hasanalpdoyduk/Test-Software-and-Bootloader-Development-for-an-ECU/Images/dspic_applicationc.pdf

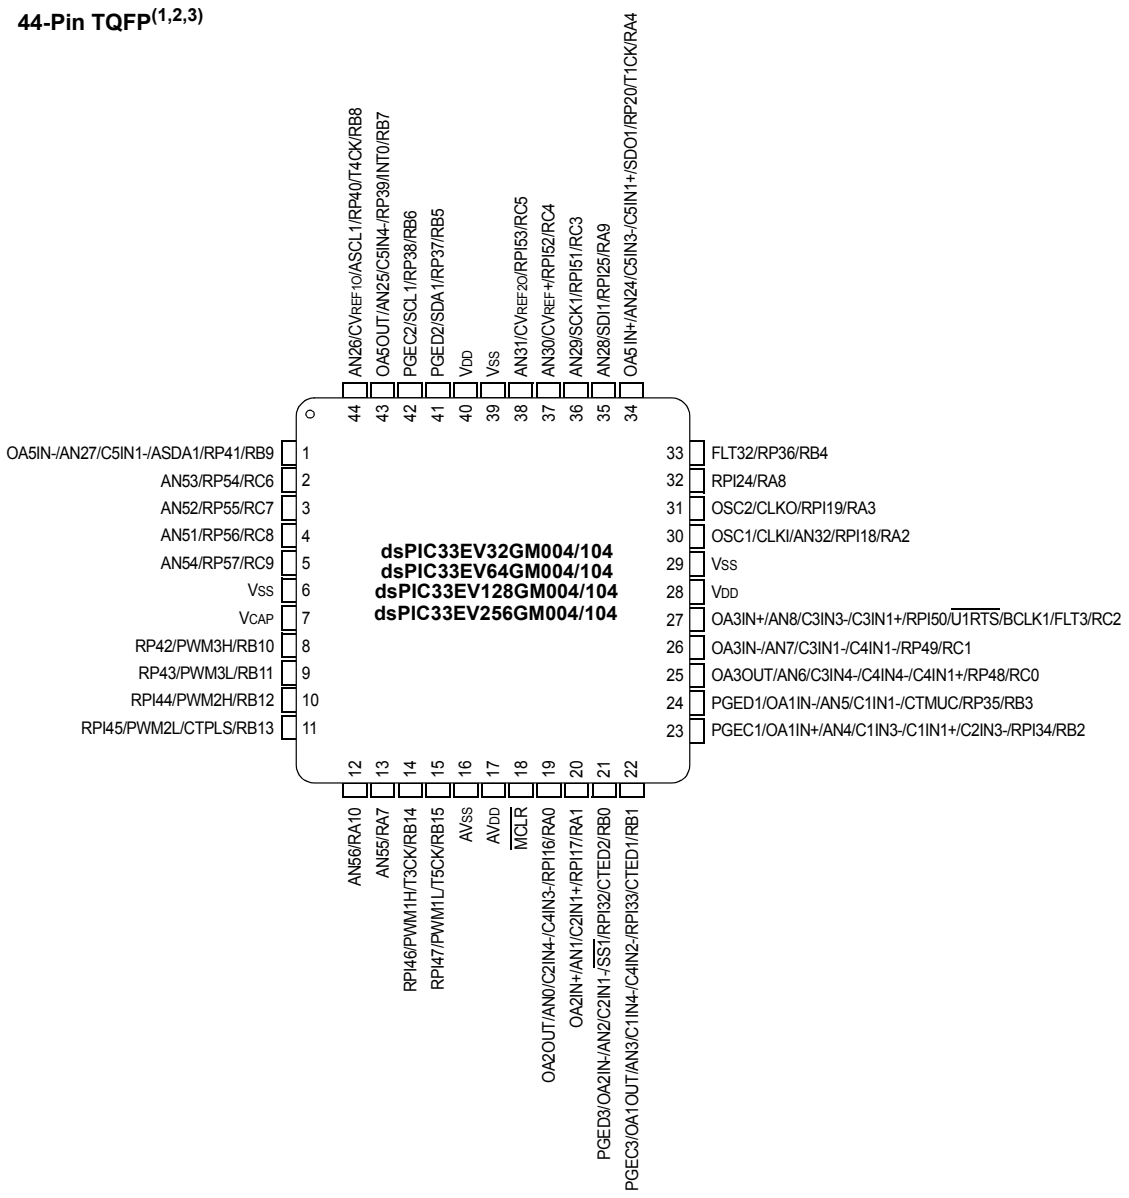
[picture p2: figure]
AN26/CVREF1O/ASCL1/RP40/T4CK/RB8 AN56/RA10; RPI45/PWM2L/CTPLS/RB13; PGEC1/OA1IN+/AN4/C1IN3-/C1IN1+/C2IN3-/RPI34/RB2; PGED1/OA1IN-/AN5/C1IN1-/CTMUC/RP35/RB3; OA3OUT/AN6/C3IN4-/C4IN4-/C4IN1+/RP48/RC0; OA3IN+/AN8/C3IN3-/C3IN1+/RPI50/U1RTS/BCLK1/FLT3/RC2; VDD; OSC1/CLKI/AN32/RPI18/RA2; OSC2/CLKO/RPI19/RA3; RPI24/RA8; FLT32/RP36/RB4; RPI46/PWM1H/T3CK/RB14; RPI47/PWM1L/T5CK/RB15; AVSS; AVDD; MCLR; OA2OUT/AN0/C2IN4-/C4IN3-/RPI16/RA0; OA2IN+/AN1/C2IN1+/RPI17/RA1; PGED3/OA2IN-/AN2/C2IN1-/SS1/RPI32/CTED2/RB0; PGEC3/OA1OUT/AN3/C1IN4-/C4IN2-/RPI33/CTED1/RB1; RPI44/PWM2H/RB12; RP43/PWM3L/RB11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
