hasanalpdoyduk/Test-Software-and-Bootloader-Development-for-an-ECU/Images/layout.pdf

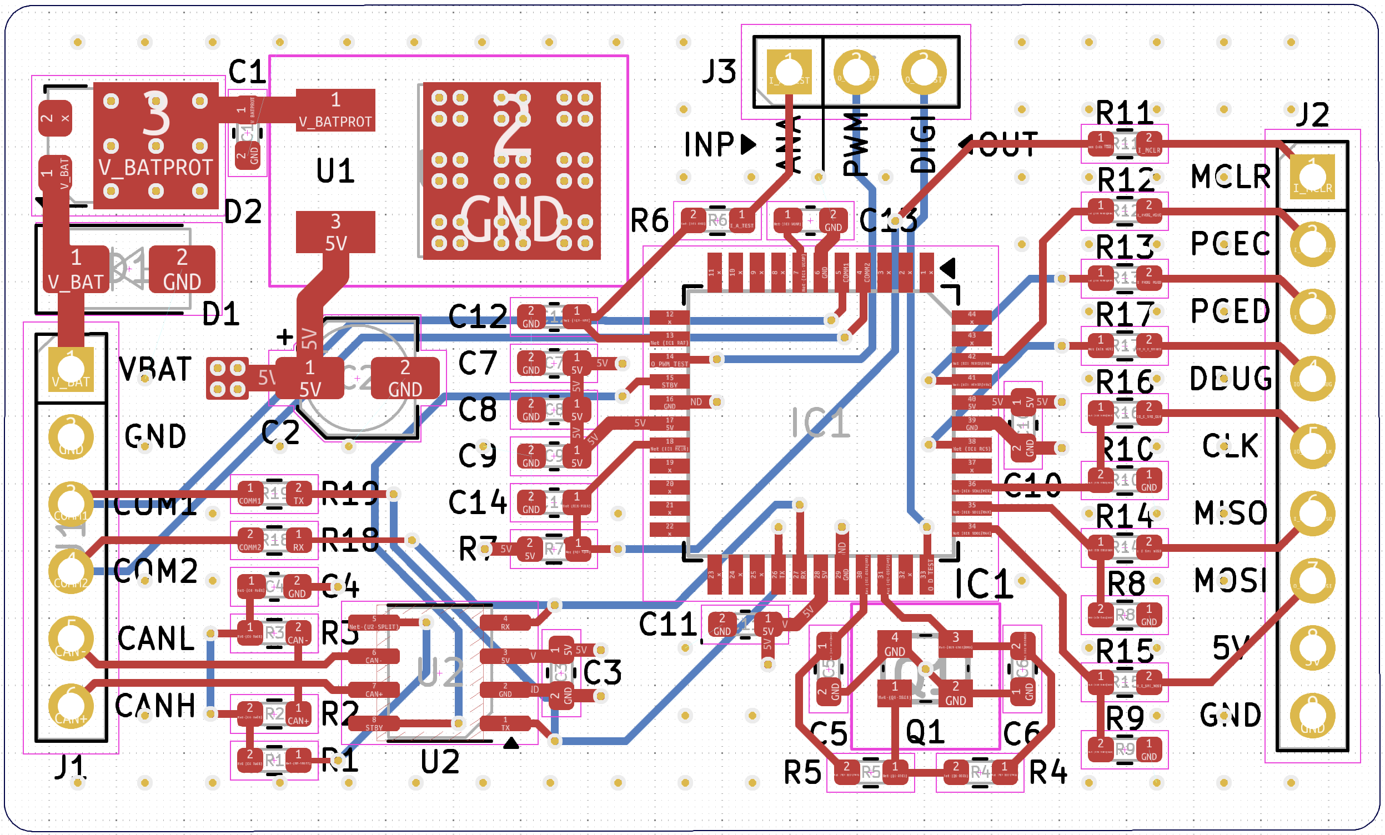
[picture p5: page 1]
