hasanalpdoyduk/Test-Software-and-Bootloader-Development-for-an-ECU/Images/pwm_wide.pdf

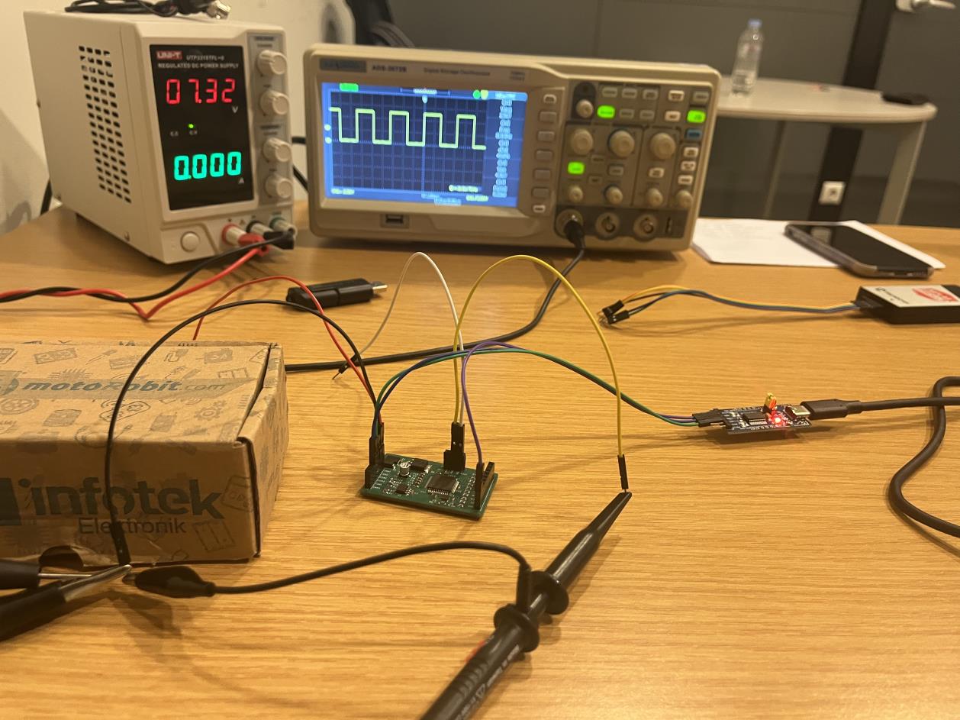
[picture p6: page 1]
