hasanalpdoyduk/Test-Software-and-Bootloader-Development-for-an-ECU/Images/rb4high_multimetre.pdf

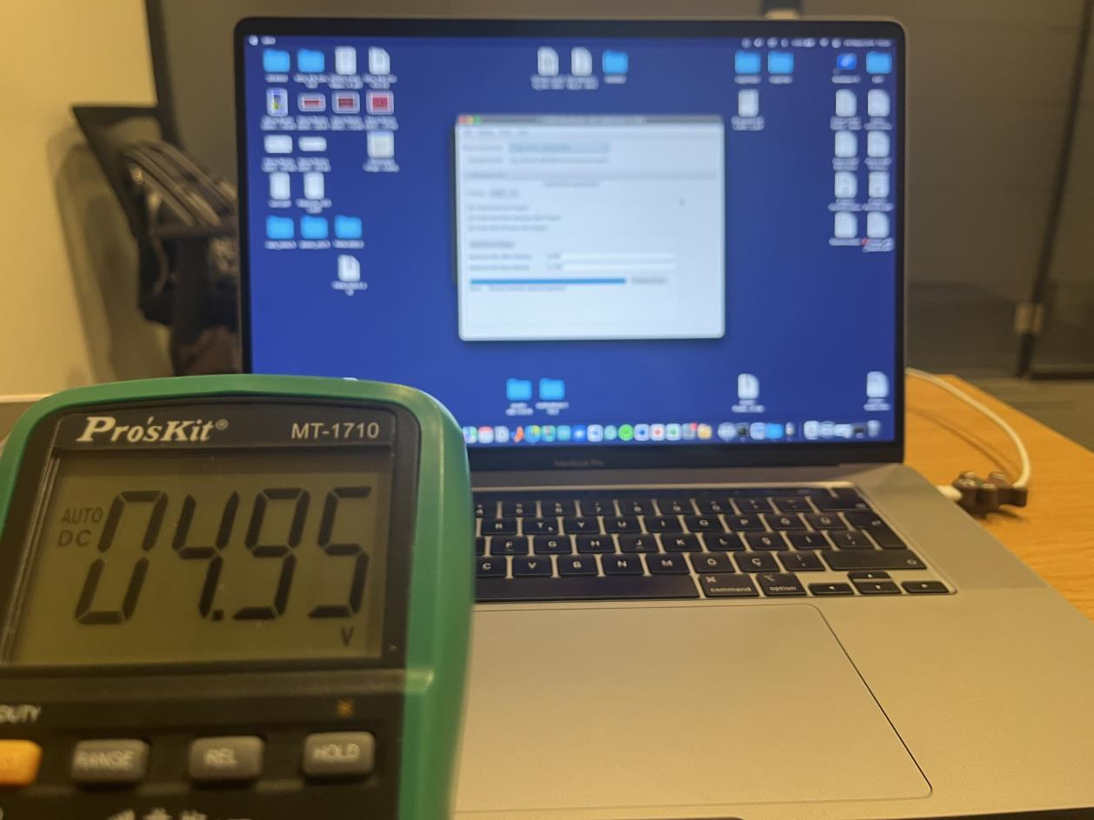
[picture p7: page 1]
