hasanalpdoyduk/Test-Software-and-Bootloader-Development-for-an-ECU/Images/rb4high_osc.pdf

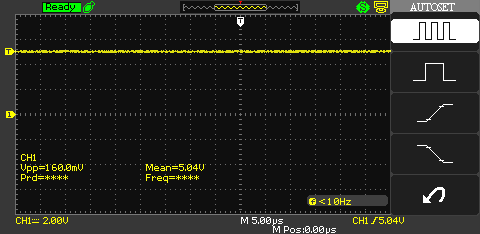
[picture p8: page 1]
