hasanalpdoyduk/Test-Software-and-Bootloader-Development-for-an-ECU/Images/simulink_0v_scope.pdf

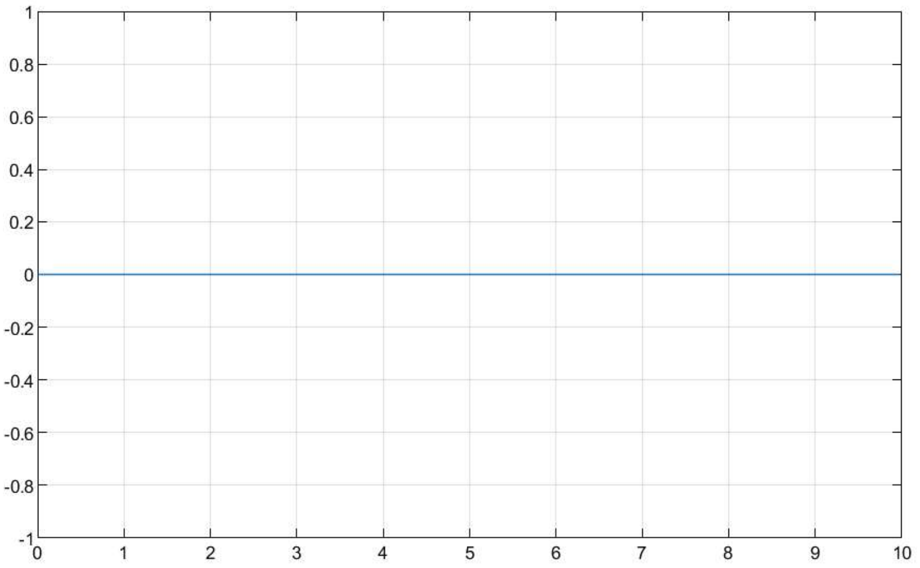
[picture p9: page 1]
