hasanalpdoyduk/Test-Software-and-Bootloader-Development-for-an-ECU/Images/simulink_5v_scope.pdf

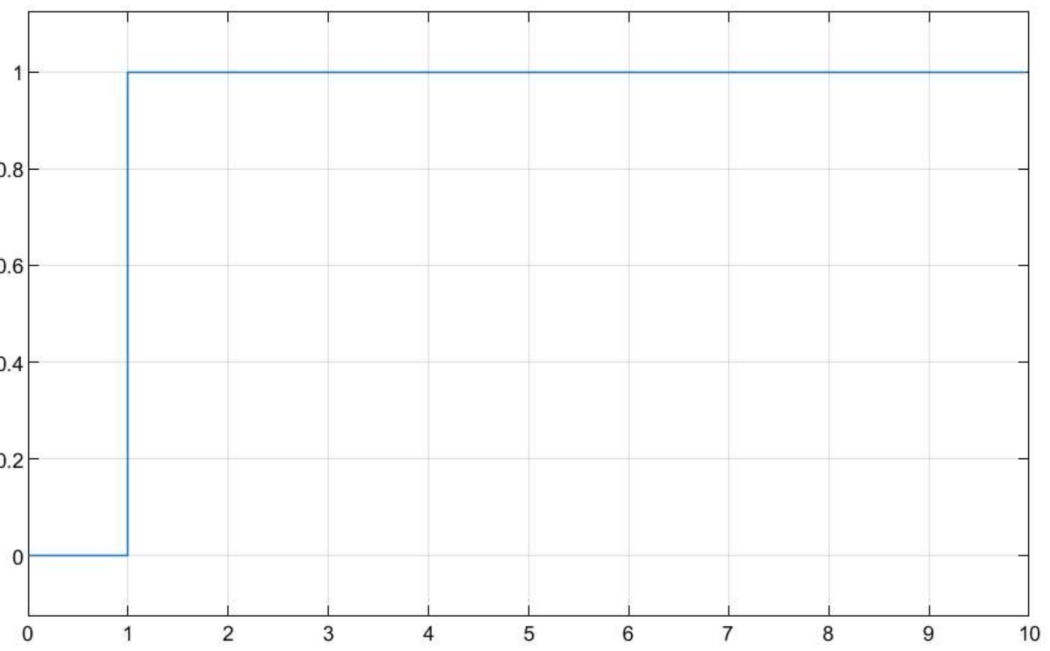
[picture p10: page 1]
