hasanalpdoyduk/Test-Software-and-Bootloader-Development-for-an-ECU/Images/basic_arch.png

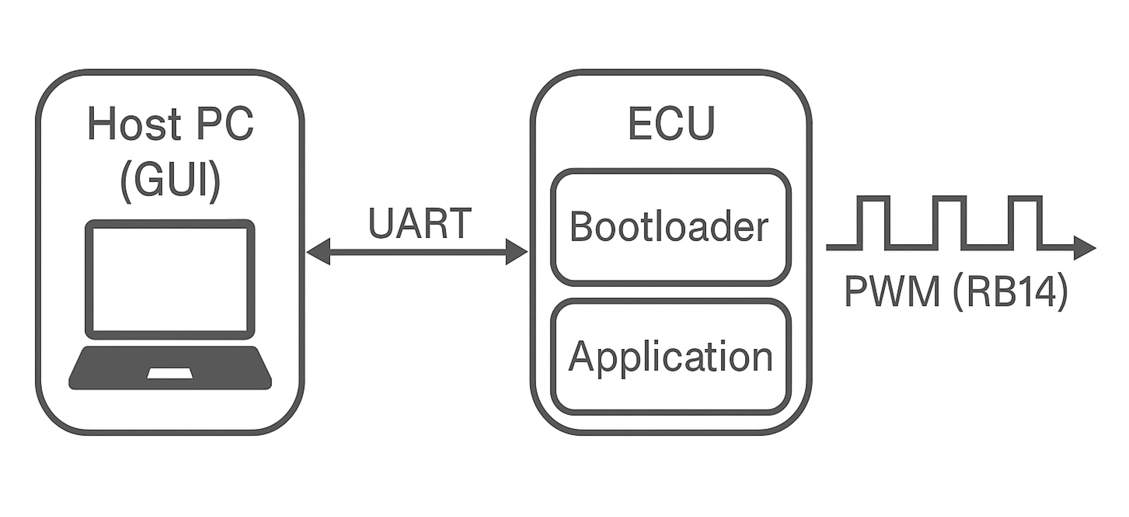
Images/basic_arch.png
