hasanalpdoyduk/Test-Software-and-Bootloader-Development-for-an-ECU/Images/board.jpg

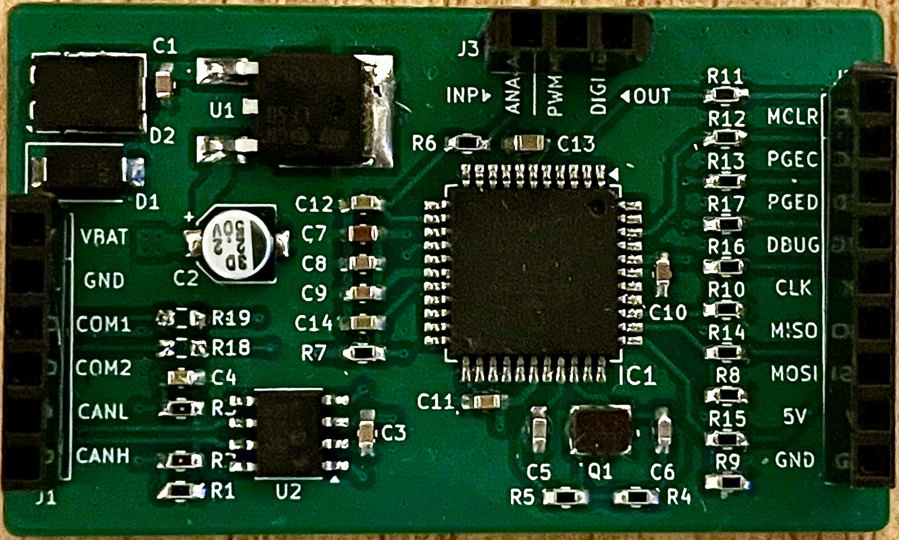
Images/board.jpg
