hasanalpdoyduk/Test-Software-and-Bootloader-Development-for-an-ECU/Images/OscillatorSs/ADS00005.BMP

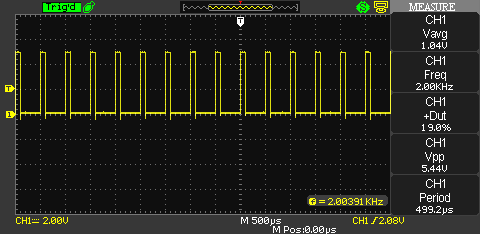
Images/OscillatorSs/ADS00005.BMP
