hasanalpdoyduk/Test-Software-and-Bootloader-Development-for-an-ECU/Images/OscillatorSs/ADS00006.BMP

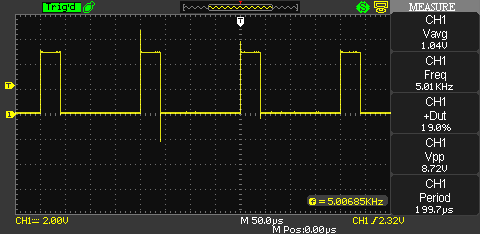
Images/OscillatorSs/ADS00006.BMP
