hasanalpdoyduk/Test-Software-and-Bootloader-Development-for-an-ECU/Images/terminal_serial_connection.png

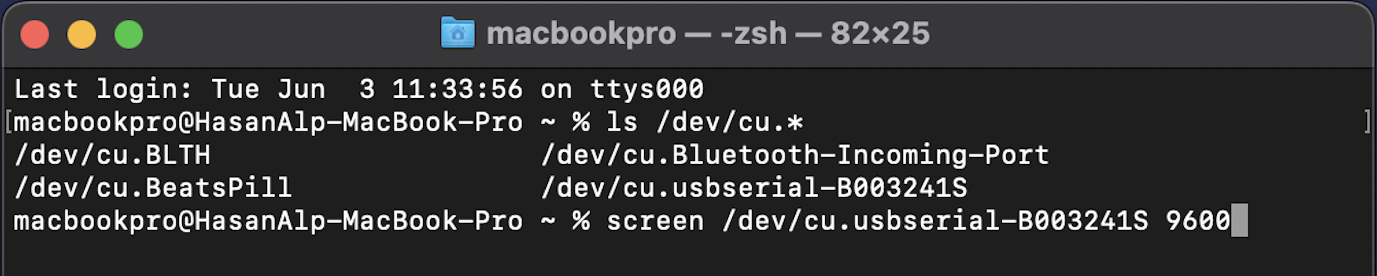
Images/terminal_serial_connection.png
