hasanalpdoyduk/Test-Software-and-Bootloader-Development-for-an-ECU/Images/terminal_UBHA_connection.png

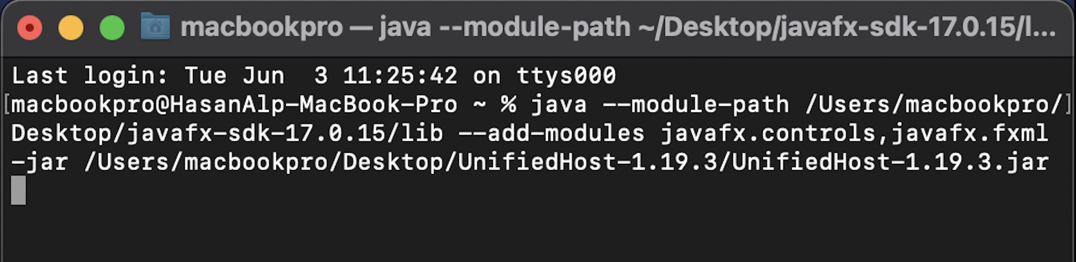
Images/terminal_UBHA_connection.png
