hasanalpdoyduk/Test-Software-and-Bootloader-Development-for-an-ECU/Images/UART1.png

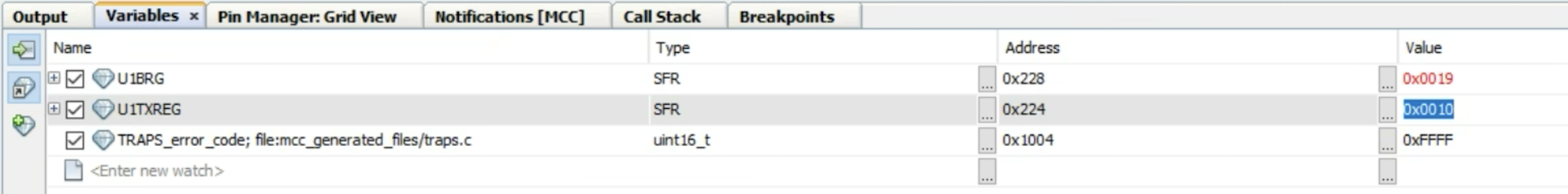
Images/UART1.png
