hasanalpdoyduk/Test-Software-and-Bootloader-Development-for-an-ECU/Images/UART_GUI_serial_port_detection.png

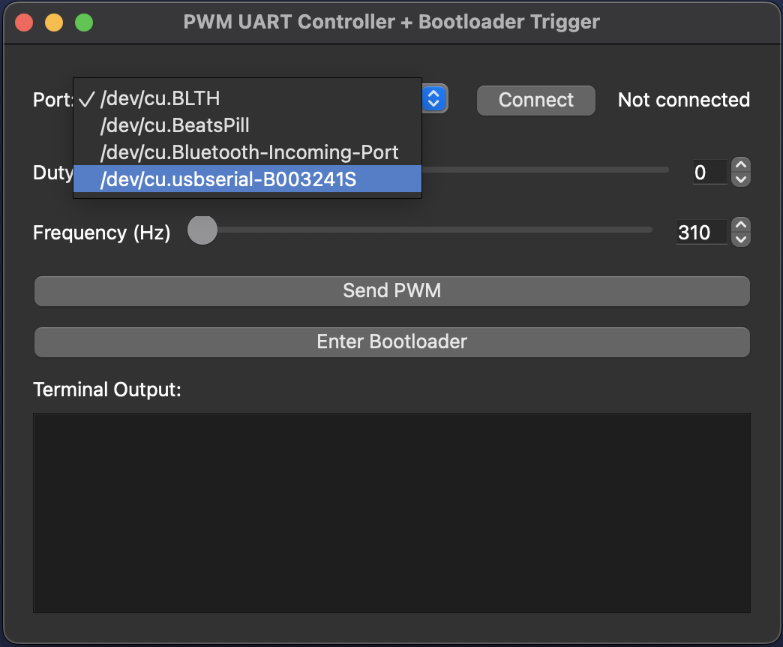
Images/UART_GUI_serial_port_detection.png
