hasanalpdoyduk/Test-Software-and-Bootloader-Development-for-an-ECU/Images/UBHA_finished.png

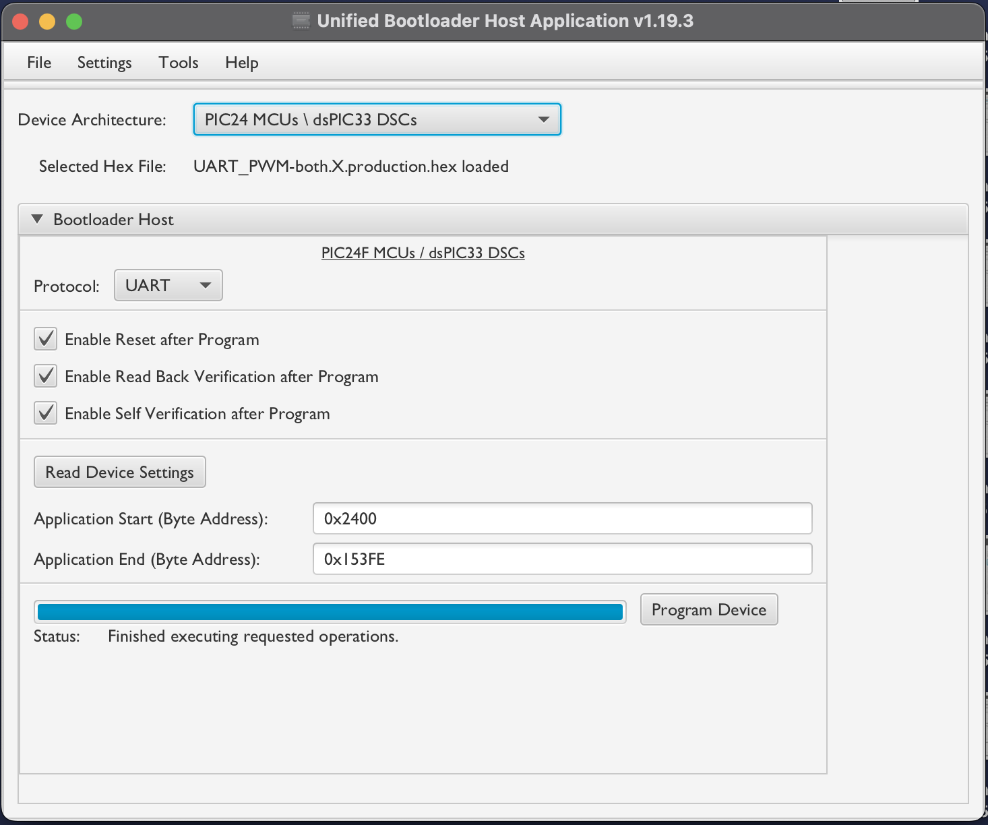
Images/UBHA_finished.png
