hasanalpdoyduk/Test-Software-and-Bootloader-Development-for-an-ECU/Images/UBHA_select1.png

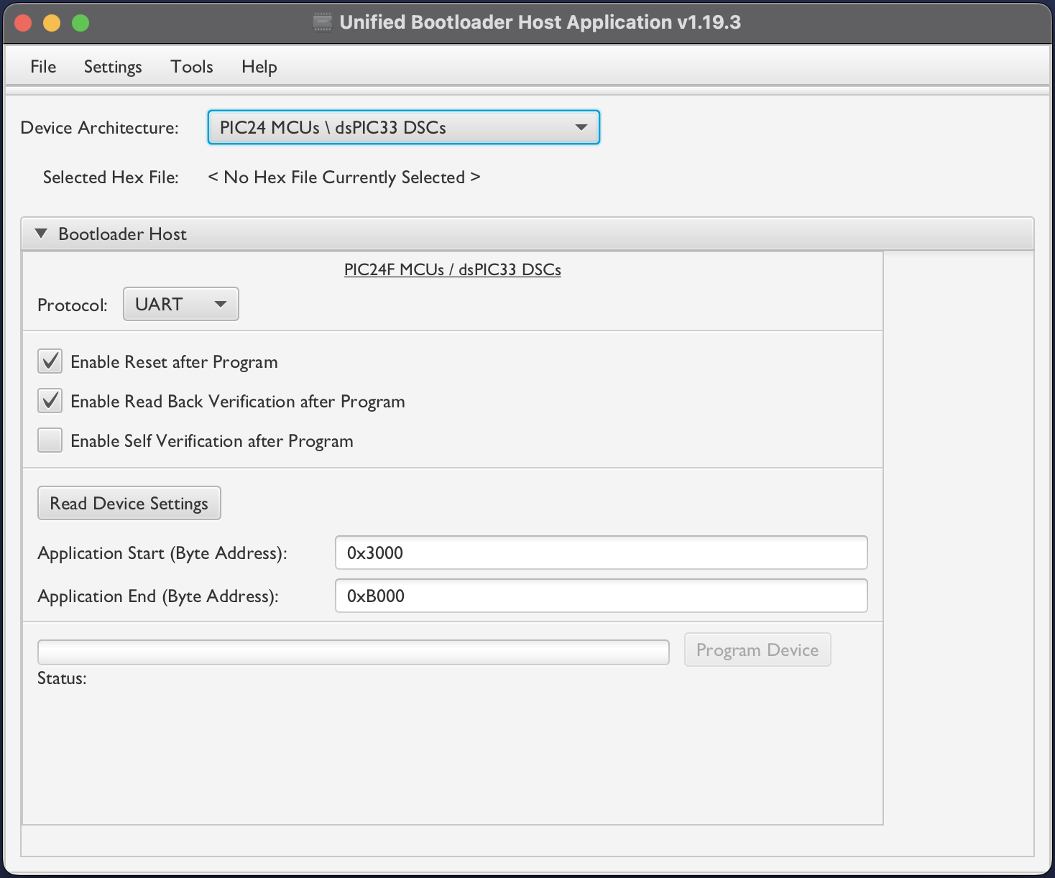
Images/UBHA_select1.png
