hasanalpdoyduk/Test-Software-and-Bootloader-Development-for-an-ECU/Images/UBHA_select_baud.png

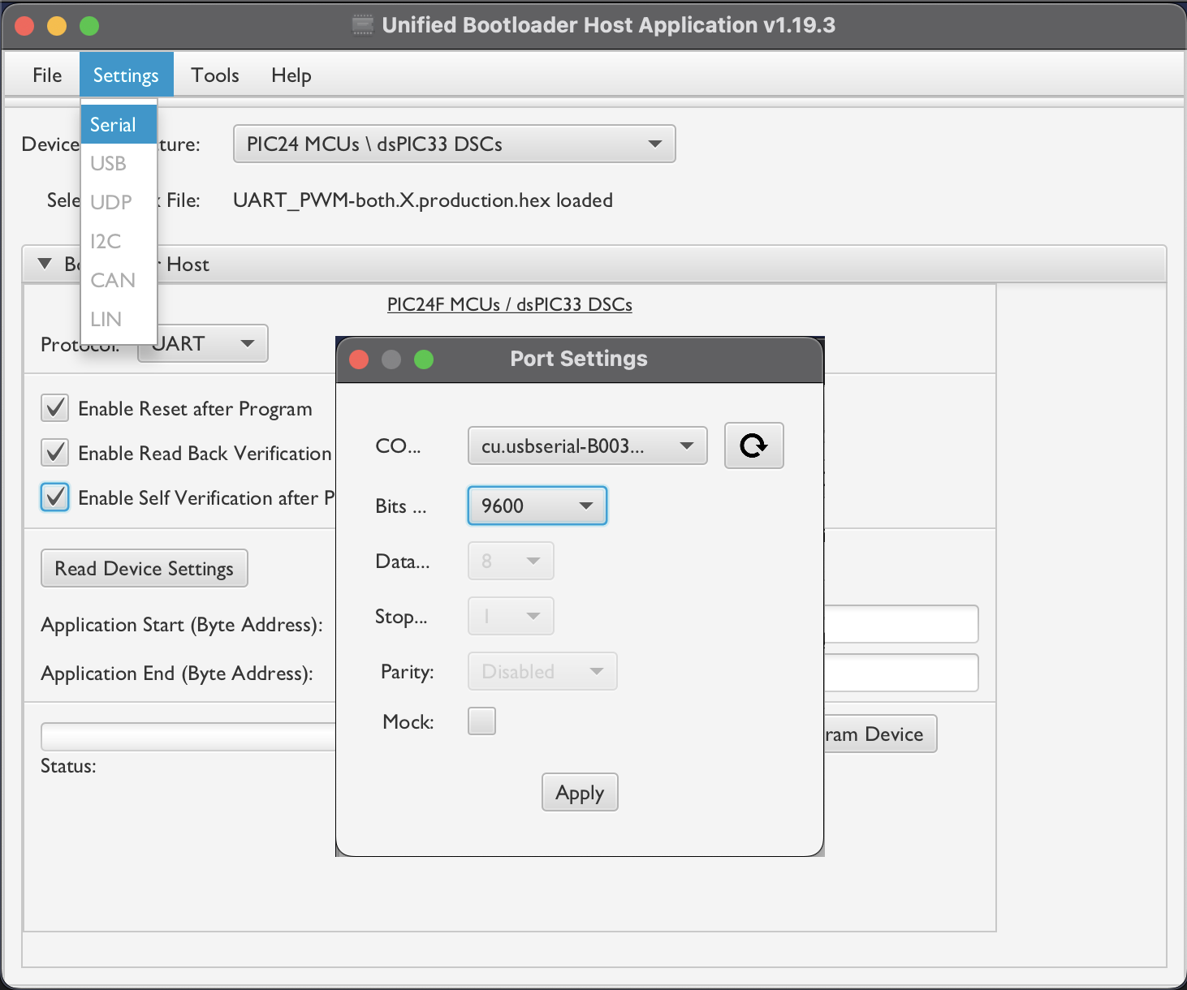
Images/UBHA_select_baud.png
