hasanalpdoyduk/Test-Software-and-Bootloader-Development-for-an-ECU/Images/digital_output_test.jpeg

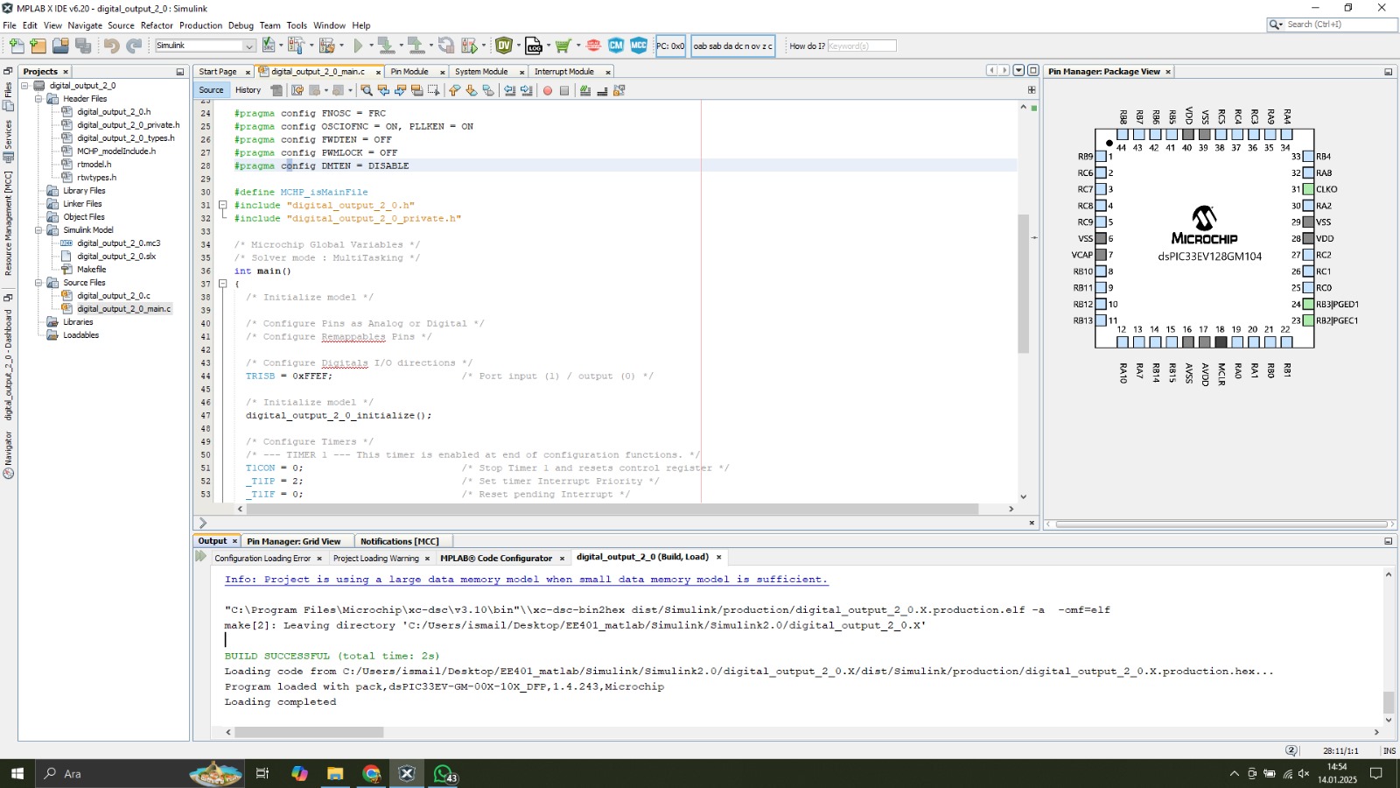
Images/digital_output_test.jpeg
