hasanalpdoyduk/Test-Software-and-Bootloader-Development-for-an-ECU/Images/ldo.pdf

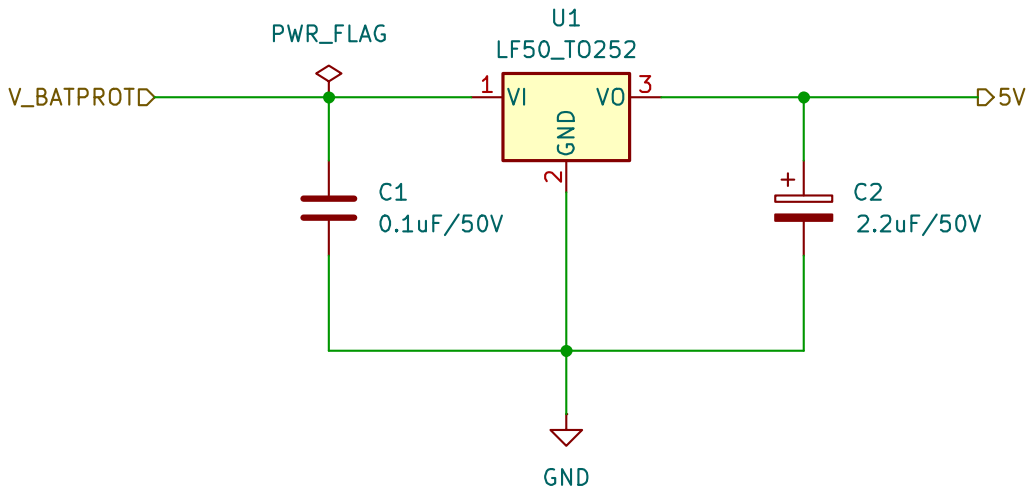
[picture p55: page 1]
