hasanalpdoyduk/Test-Software-and-Bootloader-Development-for-an-ECU/Images/mcu.pdf

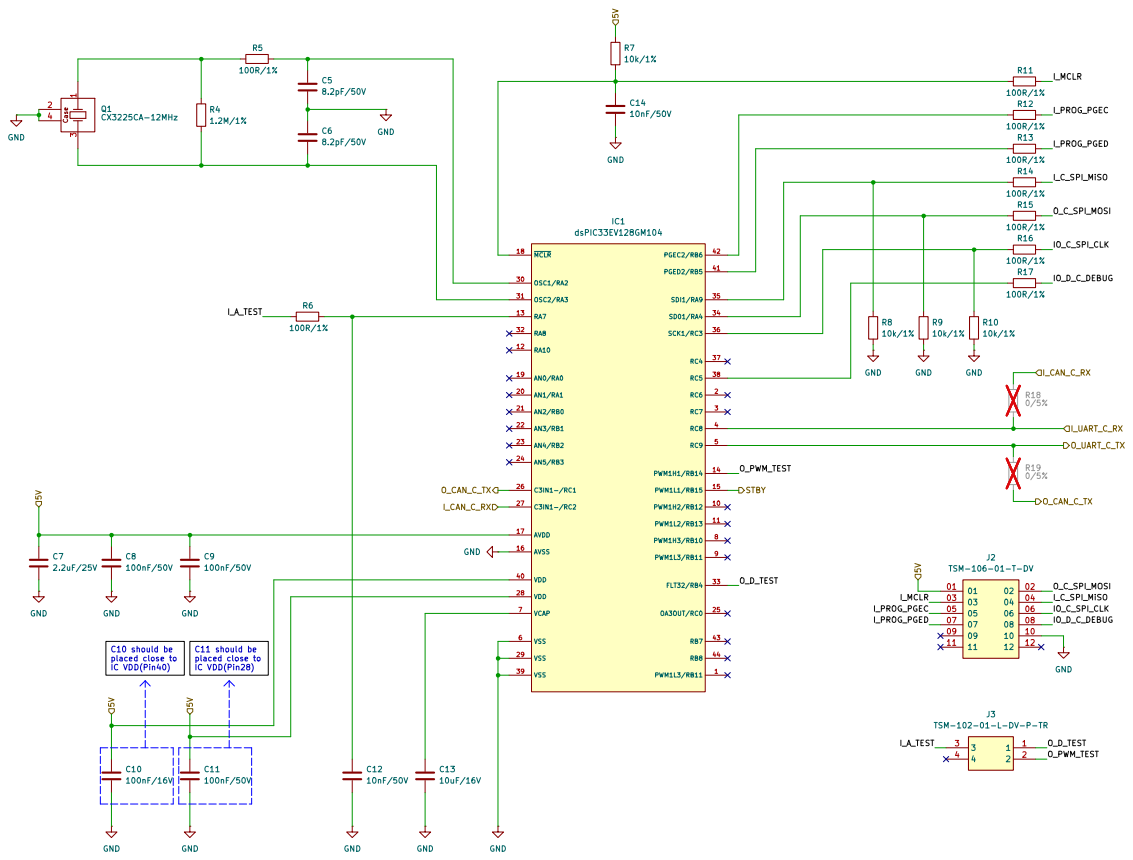
[picture p56: page 1]
