hasanalpdoyduk/Test-Software-and-Bootloader-Development-for-an-ECU/Images/protector.pdf

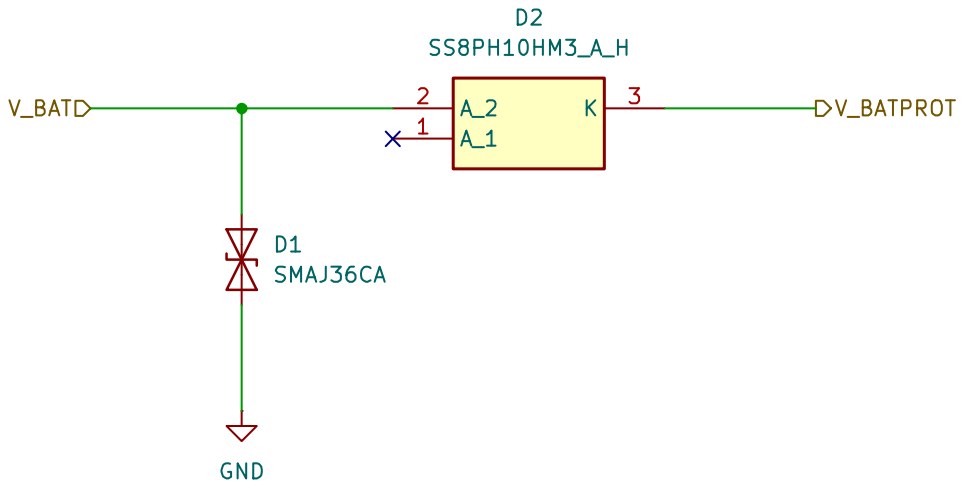
[picture p57: page 1]
