hasanalpdoyduk/Test-Software-and-Bootloader-Development-for-an-ECU/Images/root.pdf

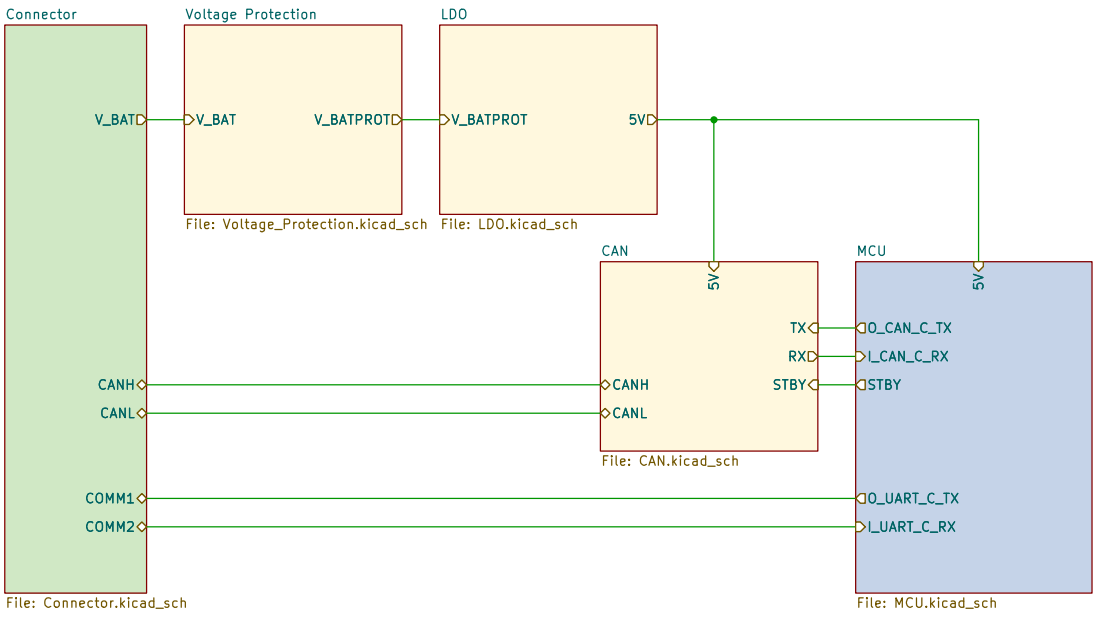
[picture p58: page 1]
