hasanalpdoyduk/Test-Software-and-Bootloader-Development-for-an-ECU/Images/root_wide.pdf

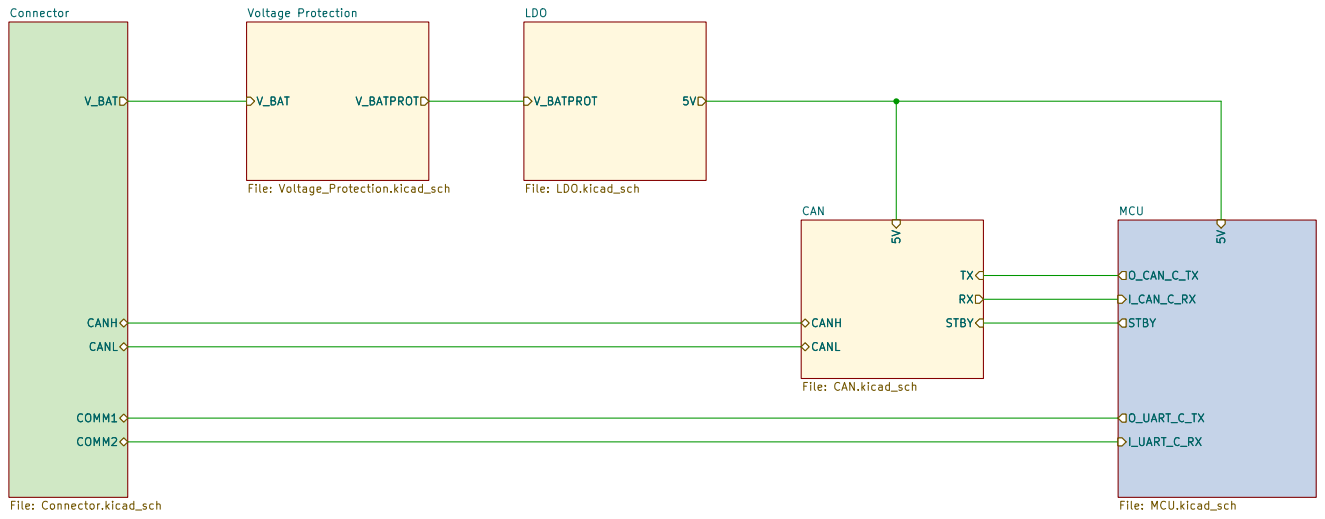
[picture p59: page 1]
