hasanalpdoyduk/Test-Software-and-Bootloader-Development-for-an-ECU/Images/simulink_digitaloutput.pdf

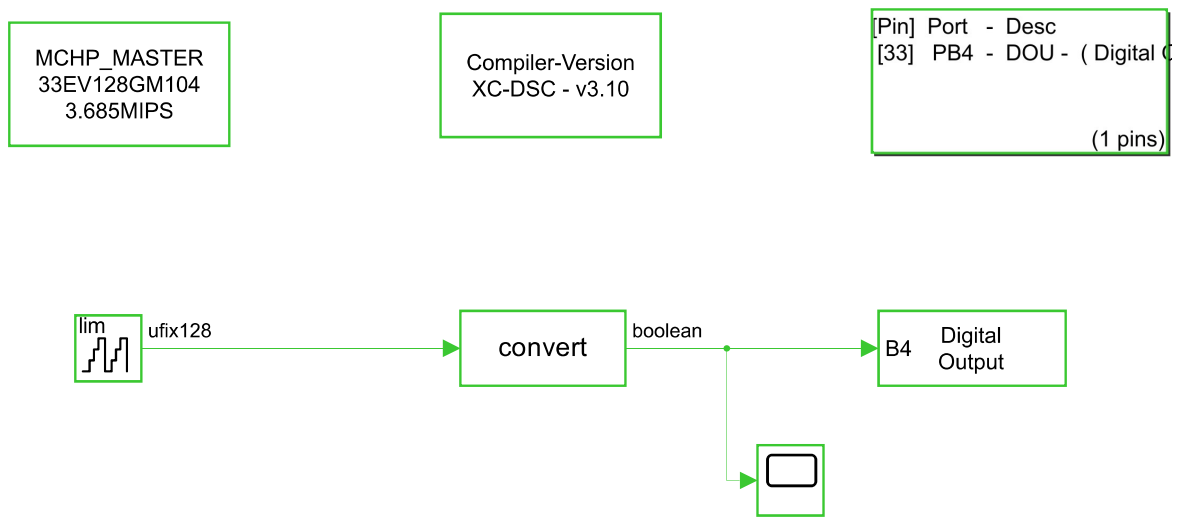
[picture p60: page 1]
